SensaGroup/StepperDriver/Docs/Output/side_view.png

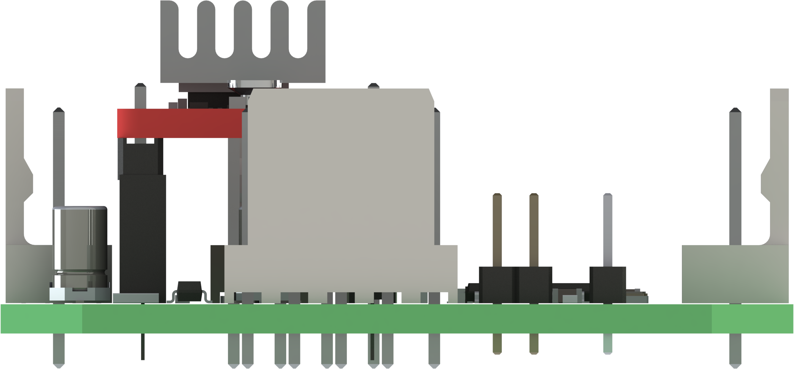
Docs/Output/side_view.png
